beyarkay/Mondrian/Phone Camera/aruco_markers/charuco_7x7.tiff

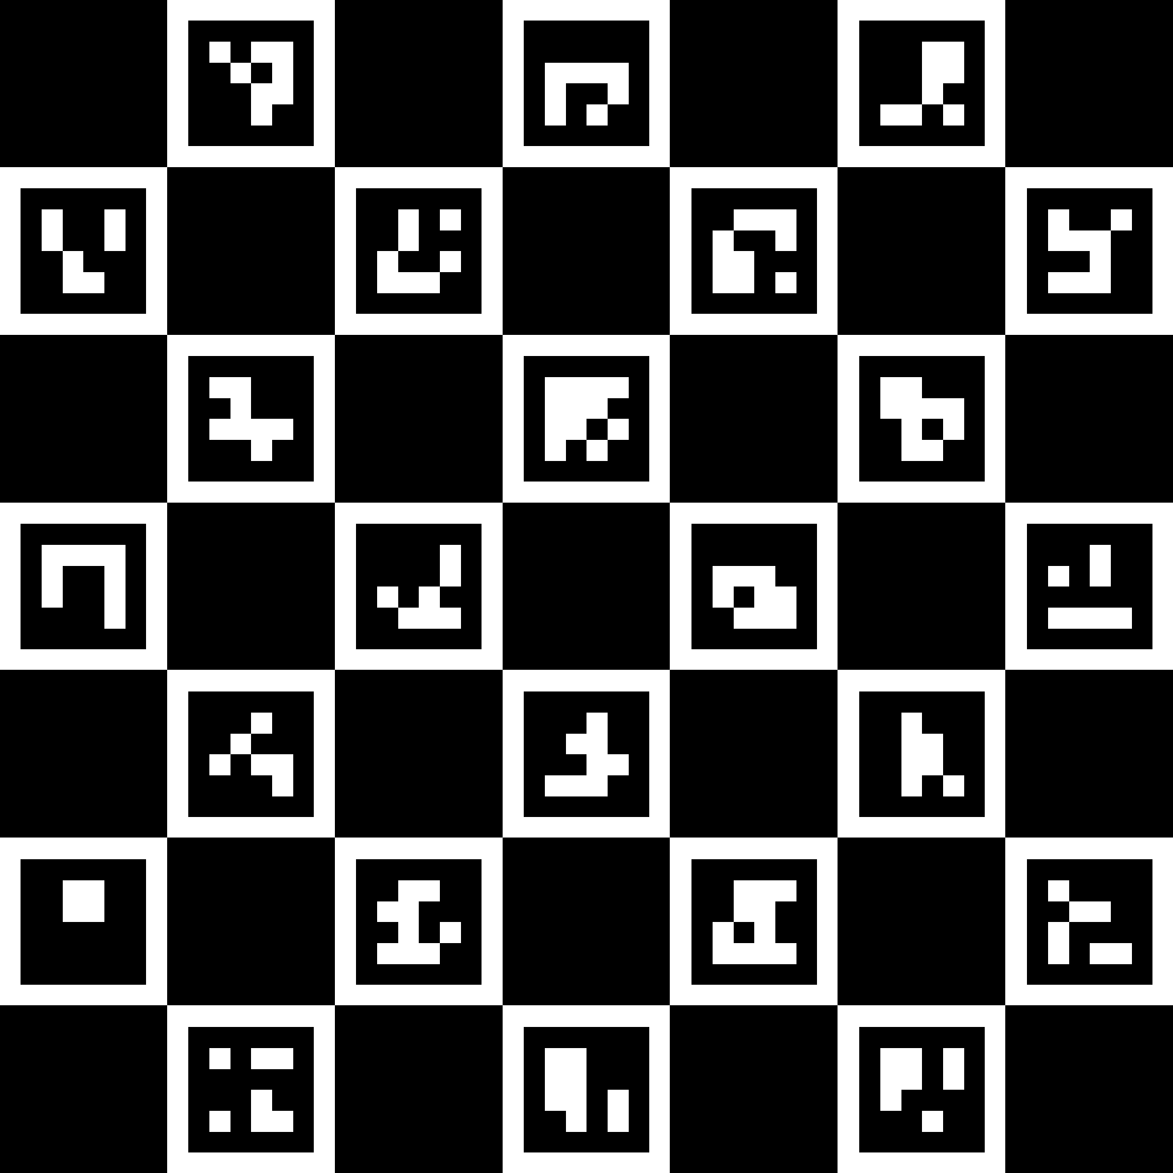
Phone Camera/aruco_markers/charuco_7x7.tiff
