beyarkay/Mondrian/Phone Camera/aruco_markers/error_hist_scaled_(460, 921).png

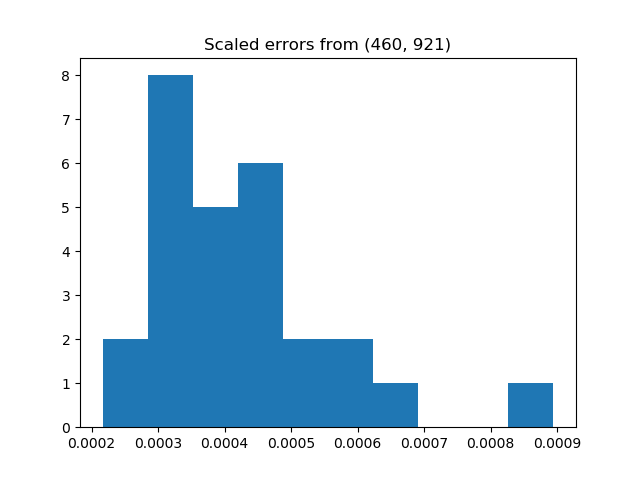
Phone Camera/aruco_markers/error_hist_scaled_(460, 921).png
