beyarkay/Mondrian/Phone Camera/aruco_markers/generated/gridboard_2x2_0.png

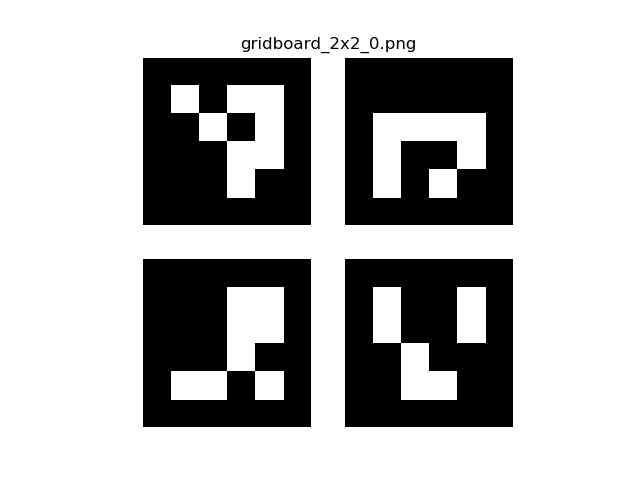
Phone Camera/aruco_markers/generated/gridboard_2x2_0.png
