beyarkay/Mondrian/Phone Camera/aruco_markers/generated/gridboard_5x5_0.png

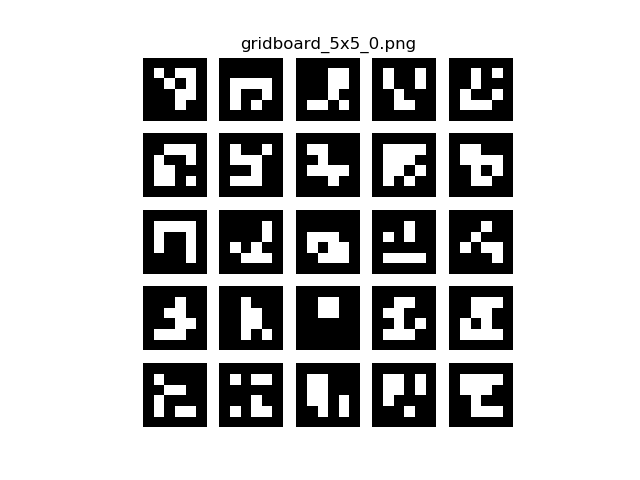
Phone Camera/aruco_markers/generated/gridboard_5x5_0.png
