beyarkay/Mondrian/Phone Camera/aruco_markers/generated/gridboard_5x5_25.png

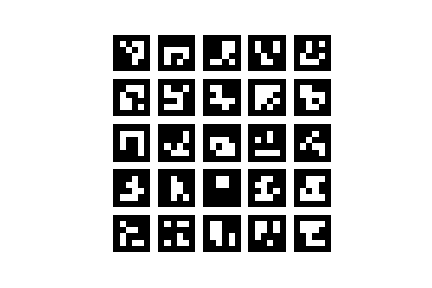
Phone Camera/aruco_markers/generated/gridboard_5x5_25.png
