beyarkay/Mondrian/Phone Camera/aruco_markers/generated/gridboards/2x2_12.png

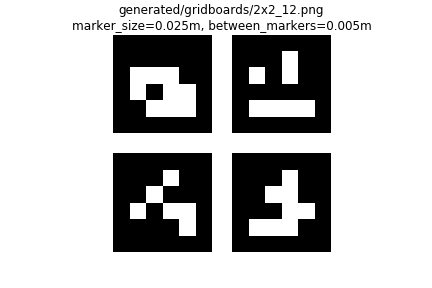
Phone Camera/aruco_markers/generated/gridboards/2x2_12.png
