beyarkay/Mondrian/Phone Camera/aruco_markers/generated/markers_3x3_0.png

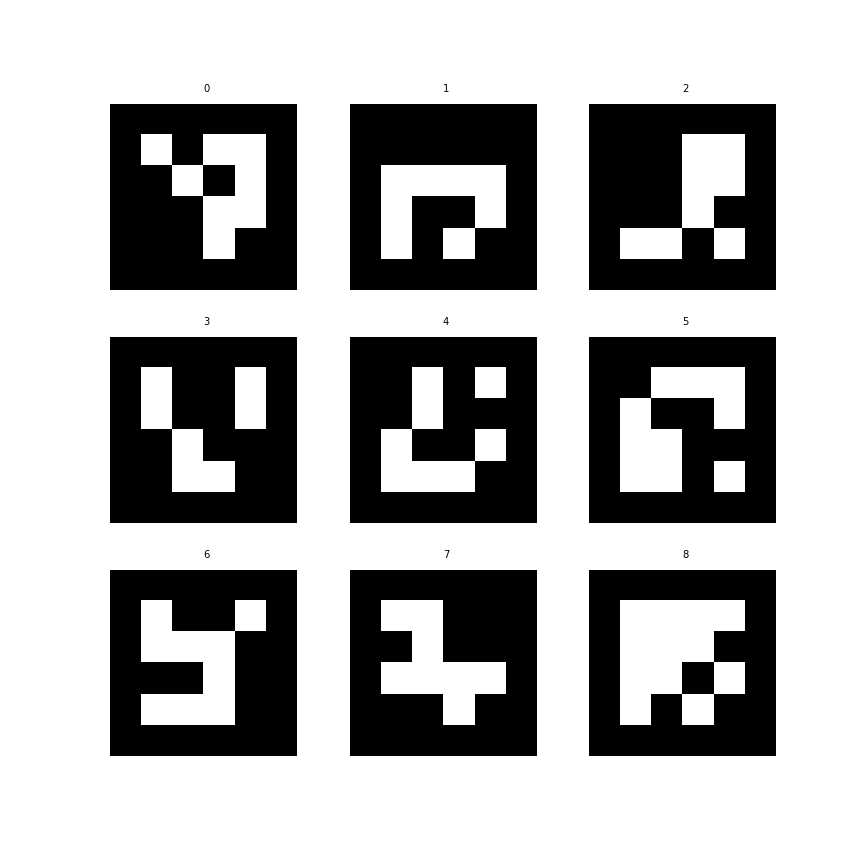
Phone Camera/aruco_markers/generated/markers_3x3_0.png
