beyarkay/Mondrian/Phone Camera/aruco_markers/generated/markers_3x3_27.png

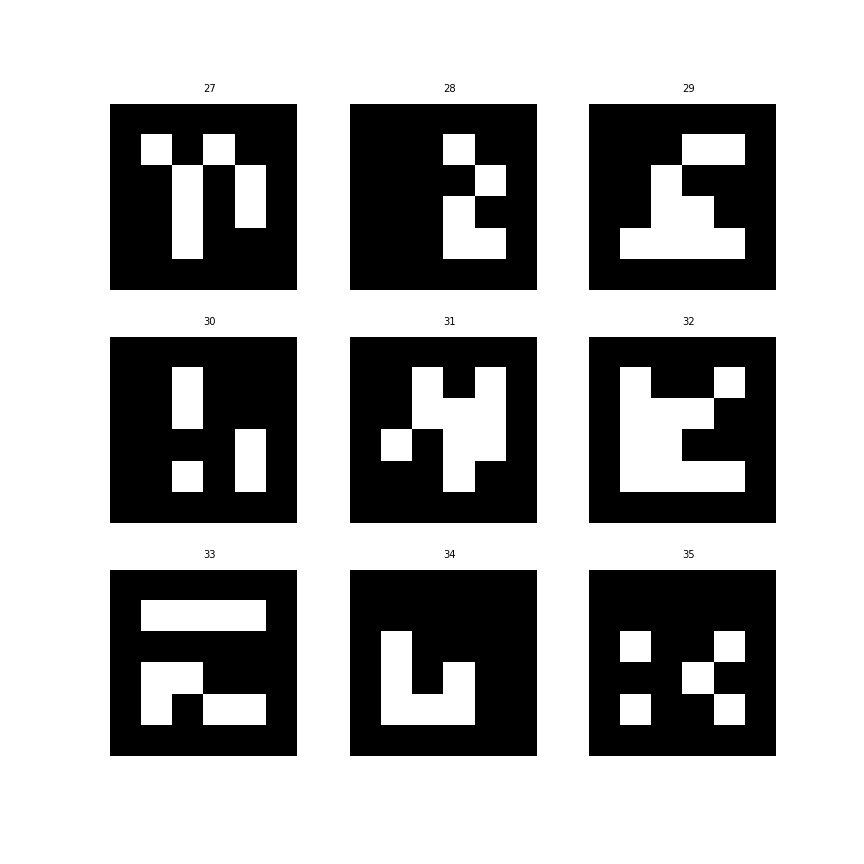
Phone Camera/aruco_markers/generated/markers_3x3_27.png
