beyarkay/Mondrian/Phone Camera/aruco_markers/generated/markers_3x3_36.png

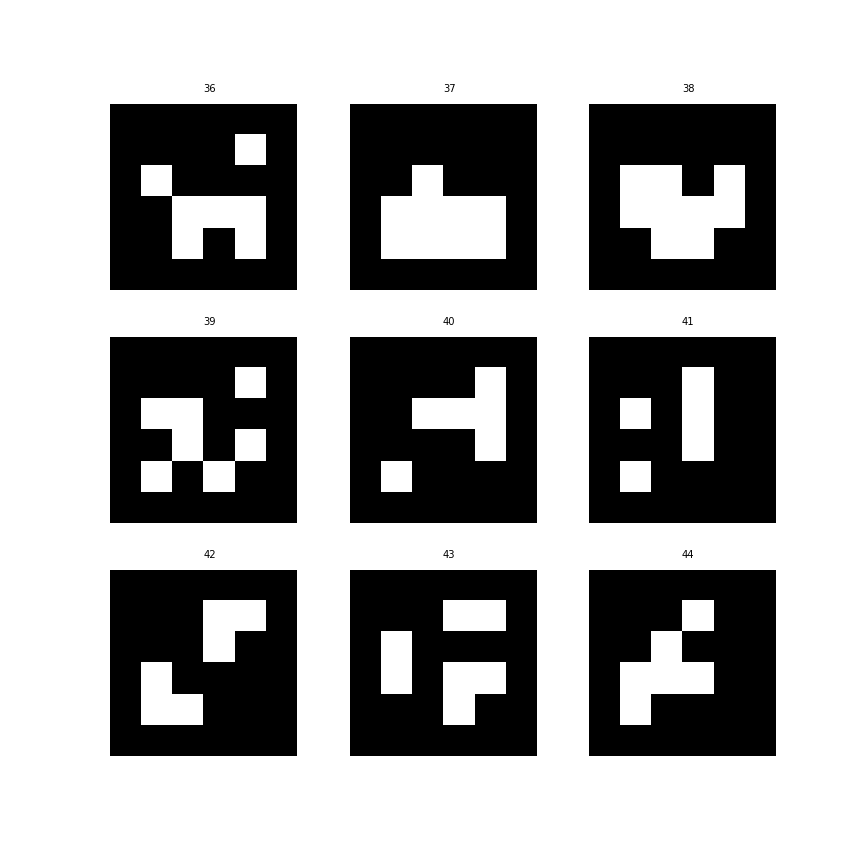
Phone Camera/aruco_markers/generated/markers_3x3_36.png
