beyarkay/Mondrian/Phone Camera/aruco_markers/generated/markers_5x5_0.png

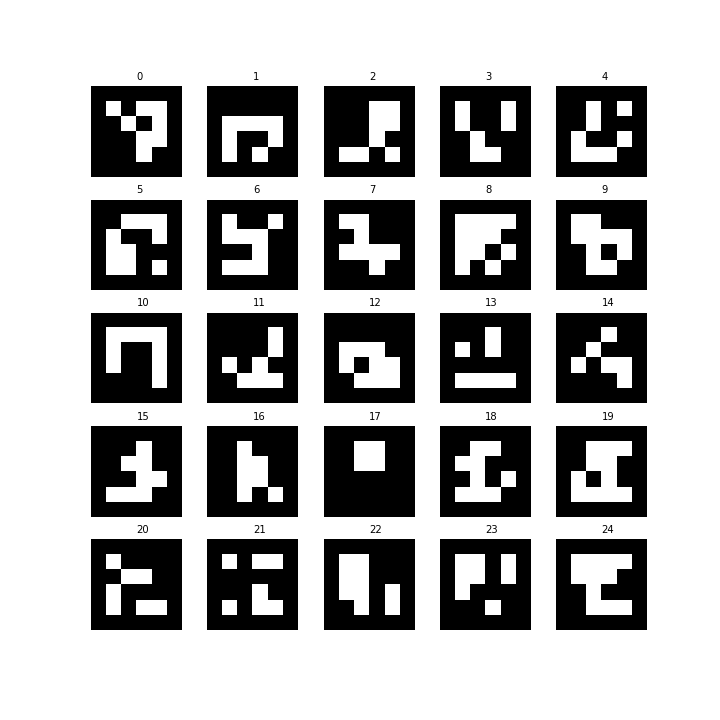
Phone Camera/aruco_markers/generated/markers_5x5_0.png
