beyarkay/Mondrian/Phone Camera/aruco_markers/generated/markers_5x5_25.png

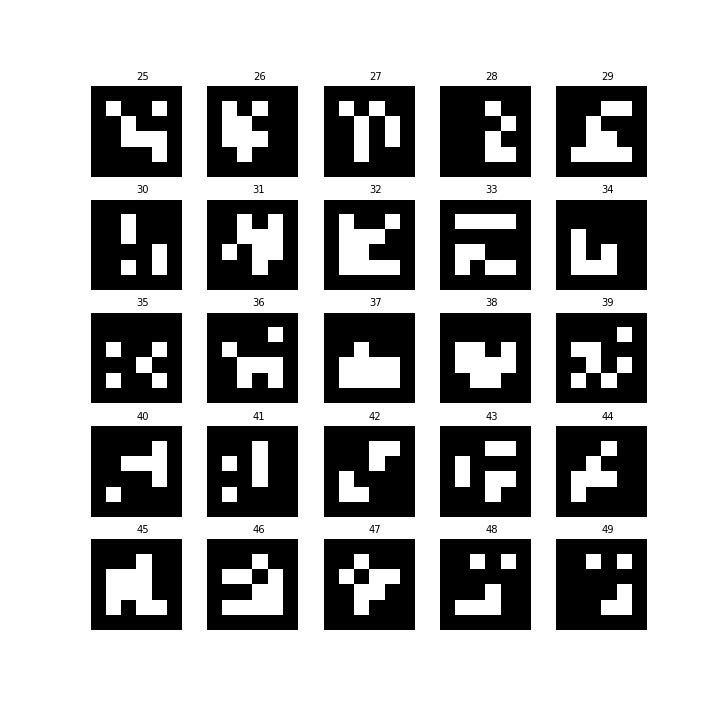
Phone Camera/aruco_markers/generated/markers_5x5_25.png
