beyarkay/Mondrian/Phone Camera/aruco_markers/gridboards_20/IMG_20191201_154723.jpg

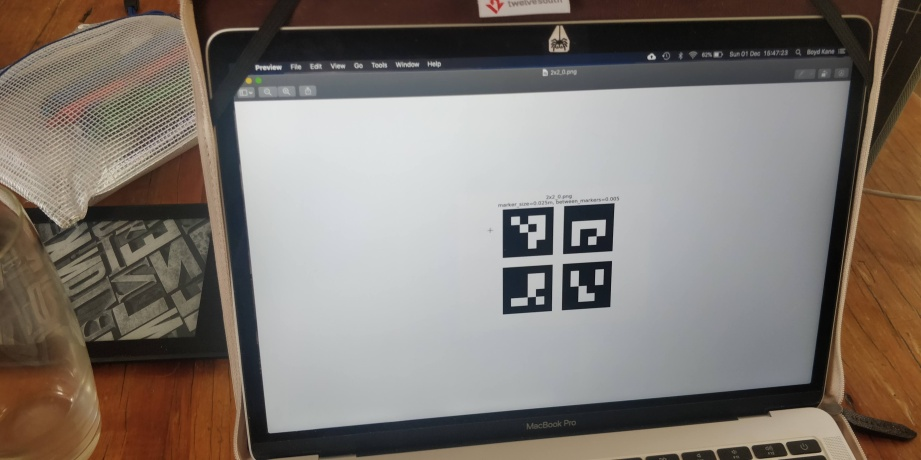
Phone Camera/aruco_markers/gridboards_20/IMG_20191201_154723.jpg
