beyarkay/Mondrian/Phone Camera/aruco_markers/gridboards_100/IMG_20191201_154726.jpg

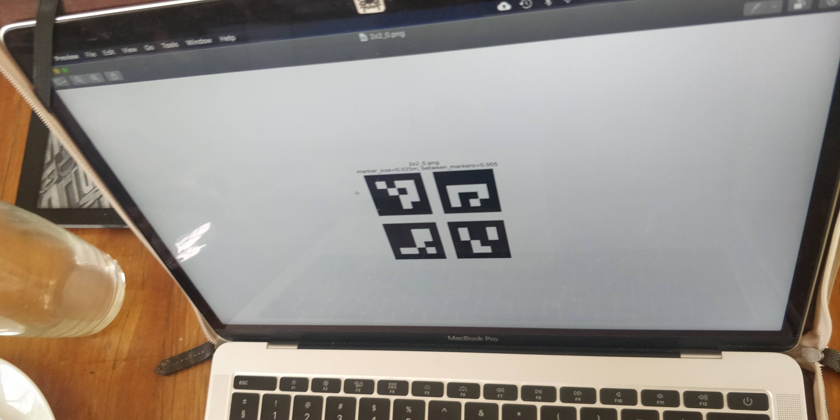
Phone Camera/aruco_markers/gridboards_100/IMG_20191201_154726.jpg
