beyarkay/Mondrian/Phone Camera/aruco_markers/gridboards_x2_100/IMG_20191202_184618.jpg

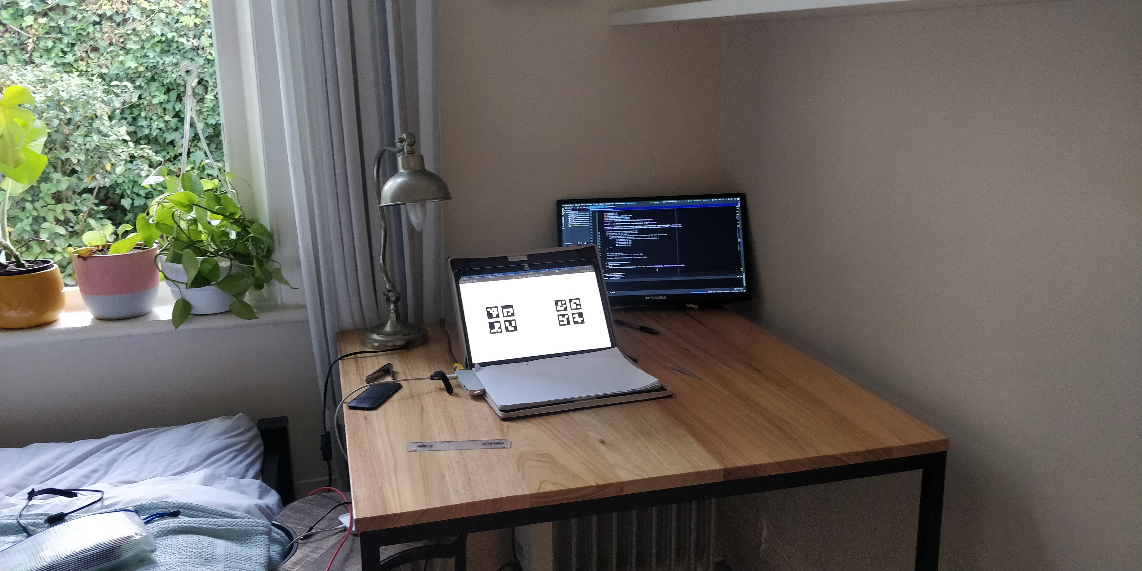
Phone Camera/aruco_markers/gridboards_x2_100/IMG_20191202_184618.jpg
