beyarkay/Mondrian/Phone Camera/aruco_markers/gridboards_x2_100/IMG_20191202_184626.jpg

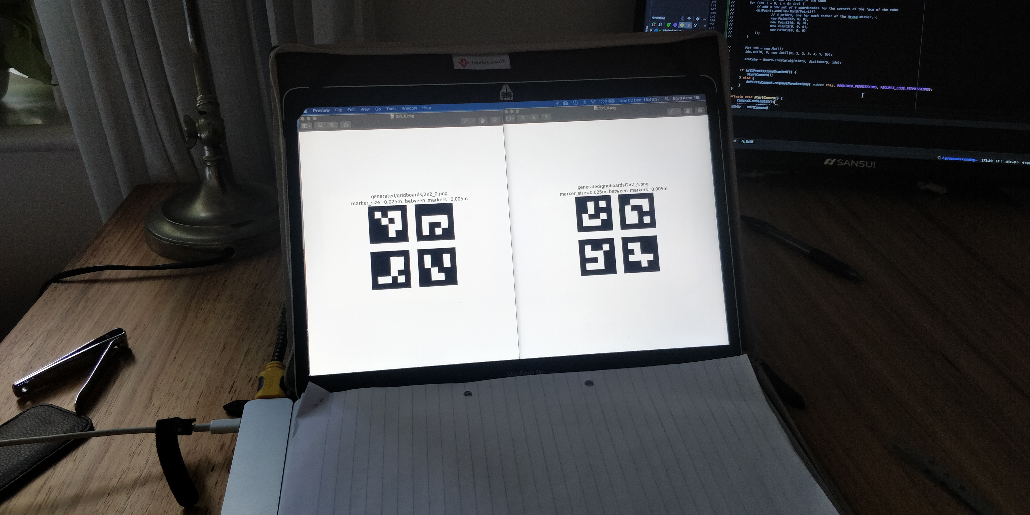
Phone Camera/aruco_markers/gridboards_x2_100/IMG_20191202_184626.jpg
