beyarkay/Mondrian/Phone Camera/aruco_markers/gridboards_x2_100/rotated/_20/IMG_20191216_174906.jpg

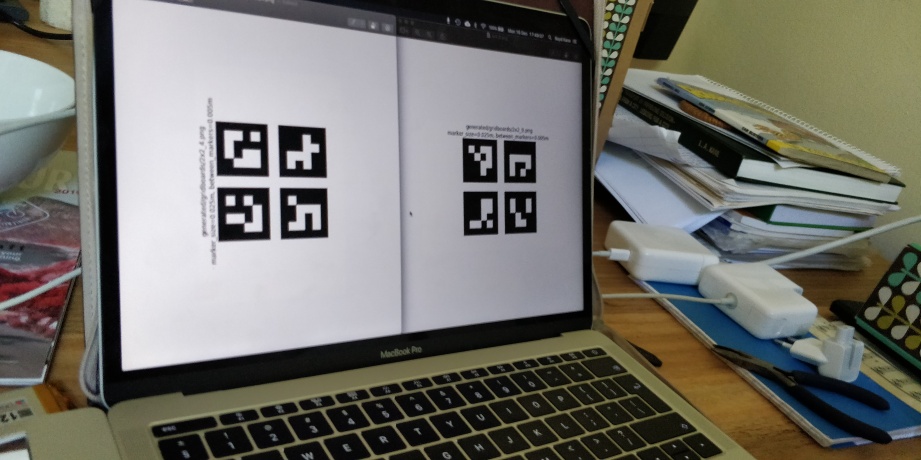
Phone Camera/aruco_markers/gridboards_x2_100/rotated/_20/IMG_20191216_174906.jpg
