beyarkay/Mondrian/Phone Camera/aruco_markers/Ret value vs compression factor.png

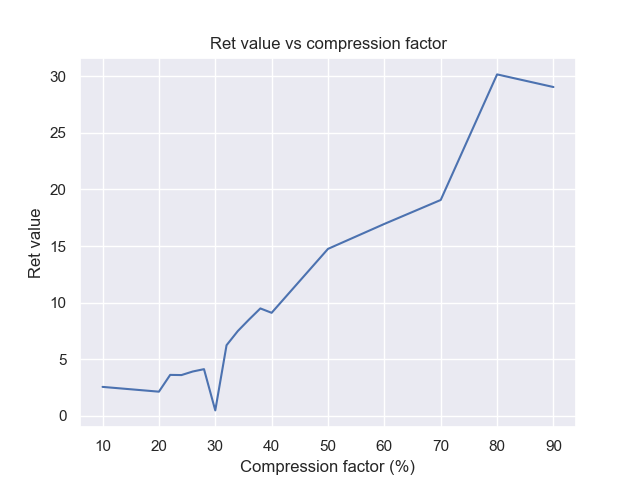
Phone Camera/aruco_markers/Ret value vs compression factor.png
