beyarkay/Mondrian/Phone Camera/aruco_markers/calibration_20/img_22.jpg

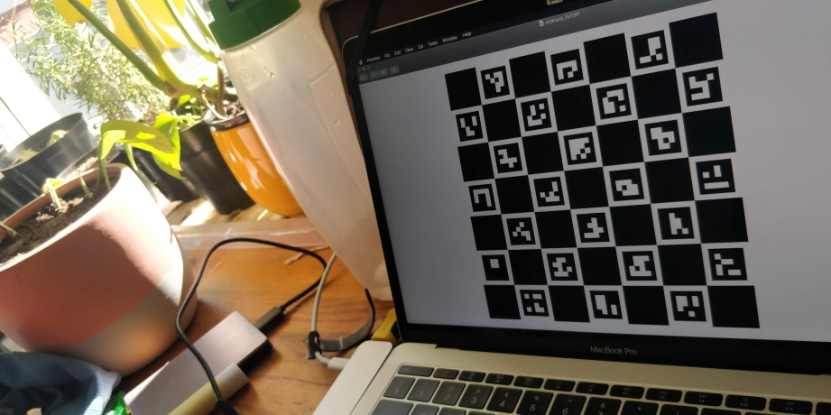
Phone Camera/aruco_markers/calibration_20/img_22.jpg
