beyarkay/Mondrian/Phone Camera/aruco_markers/calibration_20/img_23.jpg

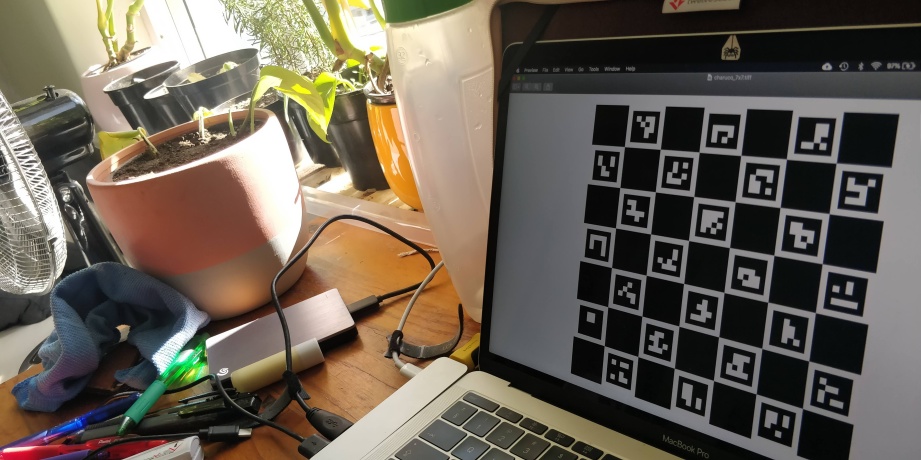
Phone Camera/aruco_markers/calibration_20/img_23.jpg
