beyarkay/Mondrian/Phone Camera/aruco_markers/calibration_20/img_29.jpg

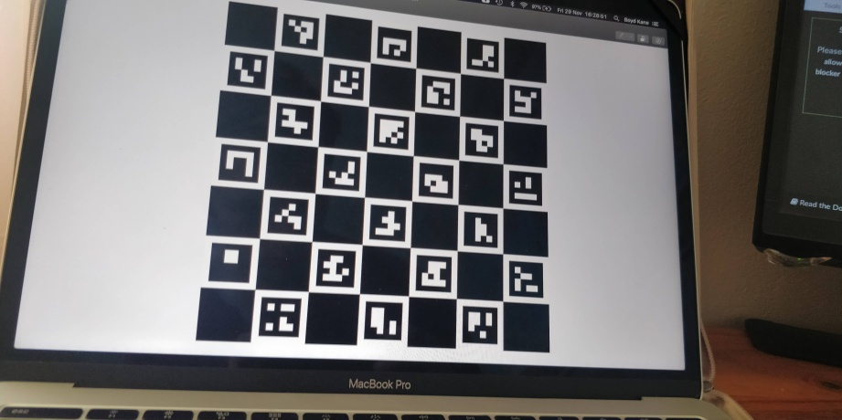
Phone Camera/aruco_markers/calibration_20/img_29.jpg
