beyarkay/Mondrian/Phone Camera/aruco_markers/calibration_20/img_32.jpg

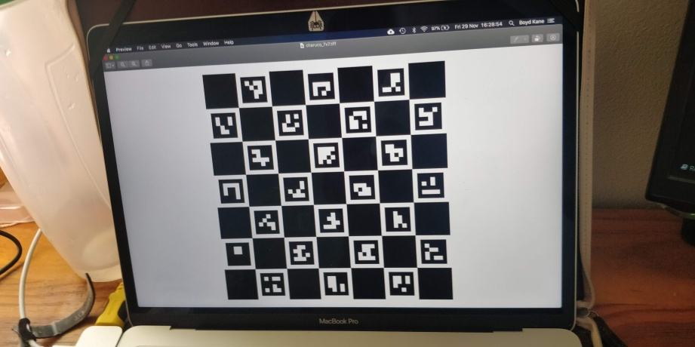
Phone Camera/aruco_markers/calibration_20/img_32.jpg
