beyarkay/Mondrian/Phone Camera/aruco_markers/calibration_100/img_33.jpg

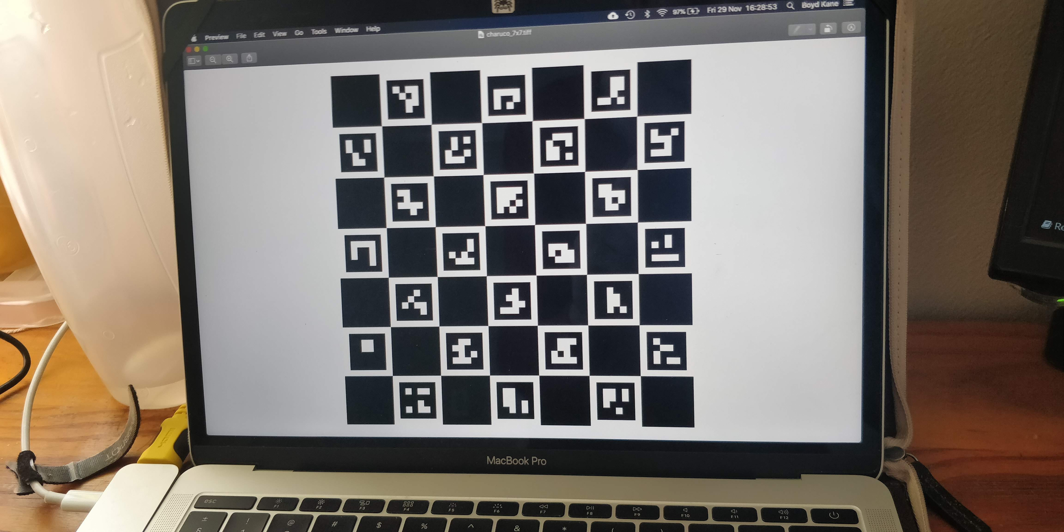
Phone Camera/aruco_markers/calibration_100/img_33.jpg
