beyarkay/Mondrian/Phone Camera/aruco_markers/calibration_photos_raw/img_10.jpg

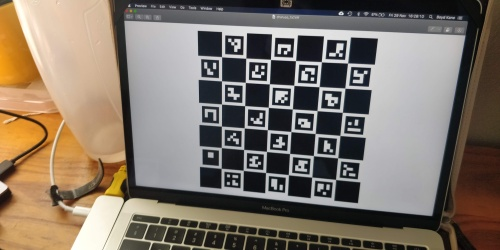
Phone Camera/aruco_markers/calibration_photos_raw/img_10.jpg
