beyarkay/Mondrian/Phone Camera/aruco_markers/calibration_photos_raw/img_12.jpg

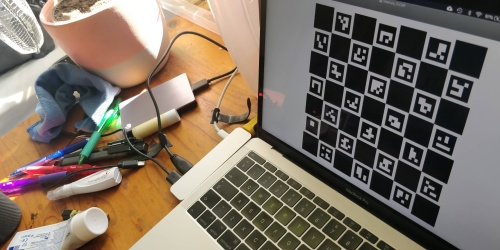
Phone Camera/aruco_markers/calibration_photos_raw/img_12.jpg
